TheFrogMouth/26-Z04-0005_The_Harp/Documents/Z04-R-0001-A_The_Harp_Design_Report/chapters/04_schematic_design.tex

\chapter{Schematic Design}\label{ch:schematic}

\section{Sheets}
The schematic is a root sheet plus seven sheets in \texttt{kicad/the\_harp/}. They were generated by \texttt{scripts/harp\_schematic/build\_layout.py} from \texttt{harp\_spec.py}. The circuits are the Timekeeper's unless noted; the bypass is The Relic's. Every pin carries a label or power symbol on a short stub (The Relic's convention). The generator re-reads its own output and traces every net against the specification: no shorts, no single-pin nets, every pin assigned. It reports 190 parts, 49 global nets and no problems. The sheets have not yet been opened in KiCad, and ERC has not been run.

\begin{table}[H]
  \small\renewcommand{\arraystretch}{1.12}
  \caption{Schematic sheets.}\label{tab:sheets}
  \begin{tabularx}{\textwidth}{@{}r >{\raggedright\arraybackslash}p{30mm} L@{}}
    \toprule
    \fmtophead{\#} & \fmtophead{Sheet} & \fmtophead{Contents} \\
    \midrule
    1 & Controls and LEDs & Pots \req{RV101}--\req{RV103} and \req{RV105} across $+$3V3, wipers through 1\,k$\Omega$ / 100\,nF to PA0, PA1, PA2, PA4; ON-ON-ON toggles \req{SW101}--\req{SW103} with both commons to GND and pins 3 and 4 to PE11--PE15 and PB10; the 0.91\,in OLED connector \req{J408} on PB6/PB7 (I$^2$C1) with 4.7\,k$\Omega$ pull-ups \\
    2 & MCU & \req{U201} STM32H750VBT6 with five 100\,nF and a 4.7\,\textmu F, two 2.2\,\textmu F VCAP, VDDA/VREF$+$ through a 220\,$\Omega$ ferrite, 25\,MHz HSE, NRST 100\,nF, BOOT0 10\,k$\Omega$, Segger needle SWD with 22\,$\Omega$; \req{U202} W25Q128 on QUADSPI bank~2 \\
    3 & Power & \req{J401} DC jack, SMAJ10CA TVS, PMEG3010 series Schottky, TPS54202 buck to $+$3V3, NCP718 LDO to $+$5V; $+$9V feeds the relay and LEDs \\
    4 & Jacks and Bypass & Four NMJ6HCD2 jacks \req{J402}--\req{J404}, \req{J406} with ESD on each; relay bypass on OUT~L (\req{K401}, G6K-2F-Y); effect and Hold LED drivers; two footswitch pad pairs \req{J405}, \req{J407} with RC filtering; expression buffer \req{U401} (MCP6001) \\
    5 & Codec & \req{IC501} AK4621EF, \req{U501} OPA2348 VCOM buffers (VCOM\_A, VCOM\_B), PDN RC, AINL and AINR from the two ADC driver channels \\
    6 & ADC Driver & \req{U601} THS4522 channels~A (left) and B (right), single-ended to differential, gain 0.59 (\req{R603}/\req{R604} and \req{R609}/\req{R610} 620\,$\Omega$) \\
    7 & Analog In and Out & \req{U701} OPA2365 L and R input buffers, \req{U702} OPA1688 difference amplifiers for L and R, output 10\,\textmu F, 100\,$\Omega$ and 1\,M$\Omega$ \\
    \bottomrule
  \end{tabularx}
\end{table}

\section{Differences from the Timekeeper}
All of these are deliberate.

\begin{itemize}
  \item \textbf{Stereo in.} Two input buffers and two ADC-driver channels; the codec's AINL and AINR are both used and nothing is parked. A mono plug grounds the IN ring and the firmware copies left to right.
  \item \textbf{ADC-driver reference.} The Timekeeper left the driver's IN\_N open. Here it goes to VCOM\_A, the DC level of the input buffer output; this is the fix recommended by the Timekeeper's input noise review (finding H1). The THS4522 stays: it is made for the single 5\,V analogue rail, with a rail-to-rail output and VOCM pinning the output common mode to the codec's VCOM. Replacing it with the spare OPA1656 half was tried and reverted on 2026-10-05.
  \item \textbf{Input op-amp OPA2365, not OPA1656} (Section~\ref{sec:inputstage}).
  \item \textbf{H2 fix.} \req{R705} (the Timekeeper's R810) is 49.9\,$\Omega$ rather than 5.1\,k$\Omega$, and \req{R602} is 1.05\,k$\Omega$ to match the signal leg, so the legs are balanced and the gain is no longer cut to about 0.16.
  \item \textbf{Gain 0.59, not 1.} At unity a hard-played humbucker already reaches ADC full scale and a synth or line source clips.
  \item \textbf{No input pad} (decision 11).
  \item \textbf{Outputs not crossed.} The Timekeeper wired AOUTR to its left output; here AOUTL is OUT~L. The channels are swapped in firmware when porting.
  \item \textbf{Output pull-downs.} 100\,$\Omega$ in series and 1\,M$\Omega$ to GND after each 10\,\textmu F (The Relic's convention), so the outputs sit at 0\,V when the DSP is muted.
  \item \textbf{QUADSPI on bank~2} (Section~\ref{sec:pinmap}).
\end{itemize}

\section{Input Stage}\label{sec:inputstage}
The Timekeeper's OPA1656 has an input range of V$-$ to V$+$ minus 2.25\,V (datasheet SBOS901C, section 6.6). On the 5\,V rail that stops at 2.75\,V, only 0.25\,V above the 2.5\,V bias. The Timekeeper's bench figures (input noise review, H2 table: peaks at $-16$\,dBFS with a gain of 0.152) put hard-played peaks at about $\pm$1.5\,V at the buffer, so positive peaks run more than 1\,V past that limit. The OPA2365 is a pin-compatible, zero-crossover, rail-to-rail-input part for 2.2 to 5.5\,V, so the 2.5\,V bias, the THS4522 and the 5\,V rail stay as they are. A 9\,V buffer supply was ruled out. The OPA2156 was rejected because its two input stages would put every positive peak across their handover step.

The Harp's input stage is the Timekeeper's, with the same values (\req{U701} = U801, \req{R705} = R810, \req{R601}/\req{R602} = R501/R502, \req{C702} = C807). The Timekeeper's input-chain simulation (\texttt{25-Z01-0001\_DSP\_Development\_Board/simulations/InputChain}) therefore covers it:

\begin{itemize}
  \item \textbf{Stability} into about 320\,pF through 49.9\,$\Omega$. The OPA2365 data sheet gives unity-gain stability to about 1\,nF and recommends 10 to 20\,$\Omega$ isolation. Simulated overshoot at the THS4522 input is at most 0.5\,\% for open-loop output resistances of 10 to 100\,$\Omega$, against 42 to 76\,\% without the resistor.
  \item \textbf{Noise} about 11\,nV/$\sqrt{\text{Hz}}$ at 1\,kHz, estimated from the data sheet's 100\,kHz and 0.1--10\,Hz figures. It adds about 0.9\,dB over the pickup and bias-resistor noise at the ADC. The 1\,kHz figure is still to be confirmed on the data sheet plot.
  \item \textbf{Gain and headroom.} The gain from the jack to the ADC is 0.59 with \req{R603}/\req{R604} at 620\,$\Omega$ (0.95 at 1\,k$\Omega$). A 4.8\,Vpp input, the most the OPA2365 can swing on 5\,V, just reaches full scale. A normally played single coil lands near $-18$\,dBFS, a hard-played humbucker near $-4$\,dBFS and a $+4$\,dBu synth near $-3$\,dBFS.
\end{itemize}

\section{MCU Pin Map}\label{sec:pinmap}
\begin{table}[H]
  \small\renewcommand{\arraystretch}{1.12}
  \caption{STM32H750VBT6 (LQFP-100) pin map.}\label{tab:pinmap}
  \begin{tabularx}{\textwidth}{@{}>{\raggedright\arraybackslash}p{28mm} >{\raggedright\arraybackslash}p{48mm} L@{}}
    \toprule
    \fmtophead{Function} & \fmtophead{Pins} & \fmtophead{Note} \\
    \midrule
    SAI1 to codec & PE2 MCLK\_A, PE4 FS\_A, PE5 SCK\_A, PE6 SD\_A, PE3 SD\_B & As the Timekeeper \\
    Codec control & PC14 CCLK, PC15 CDTI, PB8 CSN, PB4 PDN & As the Timekeeper, bit-banged \\
    QUADSPI bank~2 & PB2 CLK, PC11 BK2\_NCS, PE7--PE10 BK2\_IO0--3 & PF6--PF10 do not exist on LQFP-100, and bank~1 IO2 is only on PE2, which SAI1 MCLK takes. Single flash on bank~2 (FSEL = 1). Alternate functions to be confirmed in CubeMX \\
    Pots & PA0, PA1, PA2, PA4 (ADC1) & Mix, Sustain, Strings, Jawari; PA3 and PA5 free \\
    Expression & PB1 (ADC1) & As the Timekeeper \\
    Toggles & PE11/PE12 Tuning, PE13/PE14 Retune, PE15/PB10 Brightness & Two inputs each, internal pull-ups: up = A low B high, centre = both low, down = A high B low \\
    Footswitches & PB12 bypass, PB13 hold & Internal pull-ups, 1\,k$\Omega$ / 100\,nF RC \\
    Relay & PC10 & As the Timekeeper \\
    LEDs & PC6 effect, PC7 hold & TIM3 CH1/CH2 PWM, through 2N7002 from $+$9V \\
    OLED & PB6 SCL, PB7 SDA & I$^2$C1, 4.7\,k$\Omega$ pull-ups, \req{J408} \\
    SWD & PA13, PA14, PB3 SWO, NRST & Segger needle adapter \\
    HSE & PH0, PH1 & 25\,MHz, 8\,pF \\
    \bottomrule
  \end{tabularx}
\end{table}

Thirty-five pins remain free and carry no-connect flags (PA6--PA12, PA15, PB0, PB5--PB7, PB9--PB11, PB14--PB15, PC0--PC5, PC8--PC9, PC12--PC13, PD12--PD15, PE0--PE1, PE11, PE15). They leave room for a jack-detect line on OUT~R and a MIDI UART if either is wanted later.

\section{Items to Confirm}
\begin{itemize}
  \item QUADSPI bank~2 alternate functions (AF9/AF10) in CubeMX.
  \item The OPA2365 noise figure at 1\,kHz.
  \item ERC on the whole schematic once it is opened in KiCad.
\end{itemize}
